Rishaan2202/The-Surevival/20251218_154827.webp

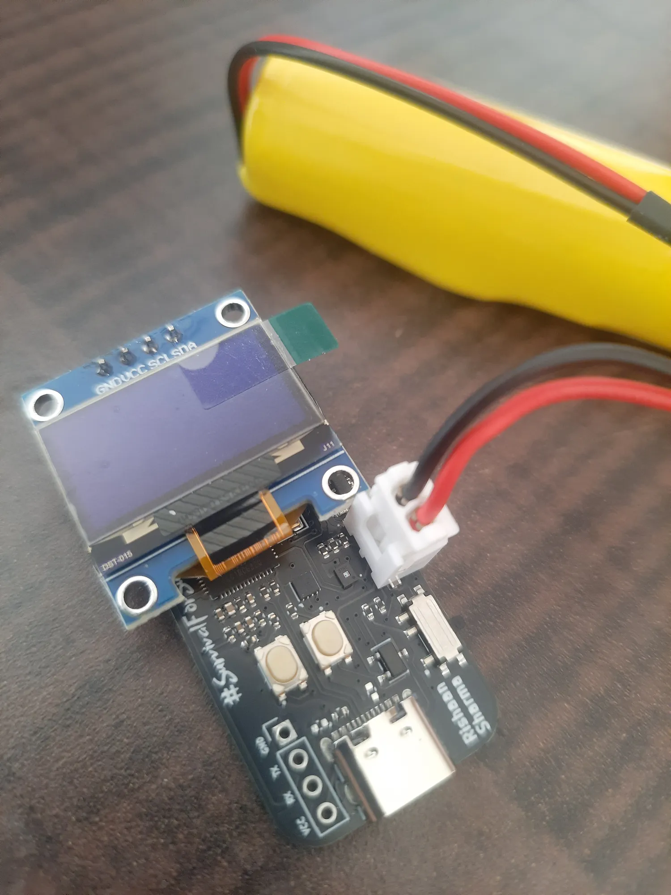
20251218_154827.webp
