Rishaan2202/The-Surevival/WhatsApp Image 2025-11-29 at 16.03.37_10fb0a49.webp

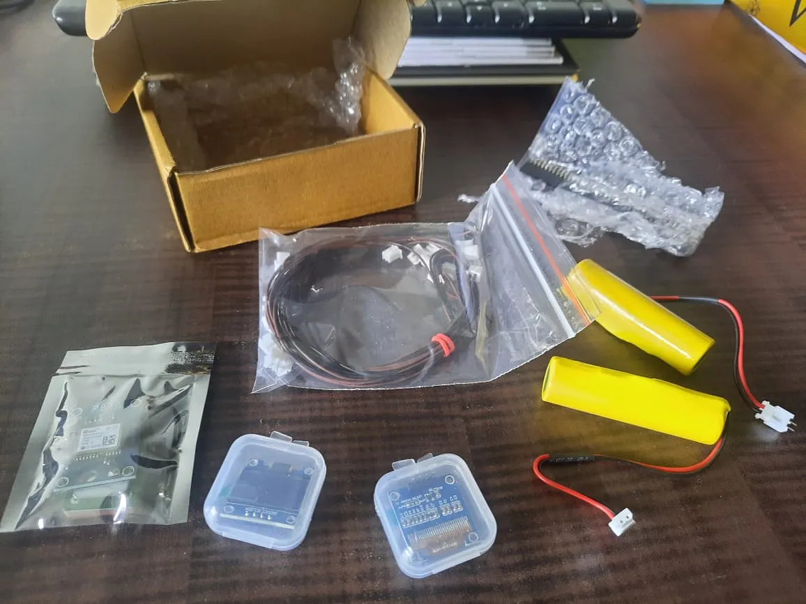
WhatsApp Image 2025-11-29 at 16.03.37_10fb0a49.webp
